doctea/sidenhancy/src/sidfreqs.cpp

#include "myfreqs.h"

// MIDI_BASE_NOTE of 57
// BASEFREQ of 440
// using PAL_PHI of 985248
// constant is 17.02841924063789
double sidinote[] = {
	16.351597831287414, // note 0 freq 16.351597831287414
	17.323914436054505, // note 1 freq 17.323914436054505
	18.354047994837977, // note 2 freq 18.354047994837977
	19.445436482630058, // note 3 freq 19.445436482630058
	20.601722307054366, // note 4 freq 20.601722307054366
	21.826764464562746, // note 5 freq 21.826764464562746
	23.12465141947715, // note 6 freq 23.12465141947715
	24.499714748859326, // note 7 freq 24.499714748859326
	25.956543598746574, // note 8 freq 25.956543598746574
	27.5, // note 9 freq 27.5
	29.13523509488062, // note 10 freq 29.13523509488062
	30.86770632850775, // note 11 freq 30.86770632850775
	32.70319566257483, // note 12 freq 32.70319566257483
	34.64782887210901, // note 13 freq 34.64782887210901
	36.70809598967594, // note 14 freq 36.70809598967594
	38.890872965260115, // note 15 freq 38.890872965260115
	41.20344461410875, // note 16 freq 41.20344461410875
	43.653528929125486, // note 17 freq 43.653528929125486
	46.2493028389543, // note 18 freq 46.2493028389543
	48.999429497718666, // note 19 freq 48.999429497718666
	51.91308719749314, // note 20 freq 51.91308719749314
	55.0, // note 21 freq 55.0
	58.27047018976124, // note 22 freq 58.27047018976124
	61.7354126570155, // note 23 freq 61.7354126570155
	65.40639132514966, // note 24 freq 65.40639132514966
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
	7458.620184289437, // note 106 freq 7458.620184289437
	7902.132820097988, // note 107 freq 7902.132820097988
	8372.018089619156, // note 108 freq 8372.018089619156
	8869.844191259906, // note 109 freq 8869.844191259906
	9397.272573357044, // note 110 freq 9397.272573357044
	9956.06347910659, // note 111 freq 9956.06347910659
	10548.081821211836, // note 112 freq 10548.081821211836
	11175.303405856126, // note 113 freq 11175.303405856126
	11839.8215267723, // note 114 freq 11839.8215267723
	12543.853951415975, // note 115 freq 12543.853951415975
	13289.750322558246, // note 116 freq 13289.750322558246
	14080.0, // note 117 freq 14080.0
	14917.240368578874, // note 118 freq 14917.240368578874
	15804.265640195976, // note 119 freq 15804.265640195976
	16744.036179238312, // note 120 freq 16744.036179238312
	17739.688382519813, // note 121 freq 17739.688382519813
	18794.54514671409, // note 122 freq 18794.54514671409
	19912.12695821318, // note 123 freq 19912.12695821318
	21096.16364242367, // note 124 freq 21096.16364242367
	22350.606811712252, // note 125 freq 22350.606811712252
	23679.6430535446, // note 126 freq 23679.6430535446
};
