doctea/sidenhancy/include/io.h

#ifndef IO__INCLUDED
#define IO__INCLUDED

#include <Encoder.h>
#include <Bounce2.h>

//Encoder knob(ENCODER_KNOB_L, ENCODER_KNOB_R);
//Bounce pushButtonA = Bounce(PIN_BUTTON_A, 10); // 10ms debounce

#endif
